nagius/DoubleClock/schematics/doubleClock.kicad_sch

## KiCad design schematics/doubleClock.kicad_sch (2024-07-17)

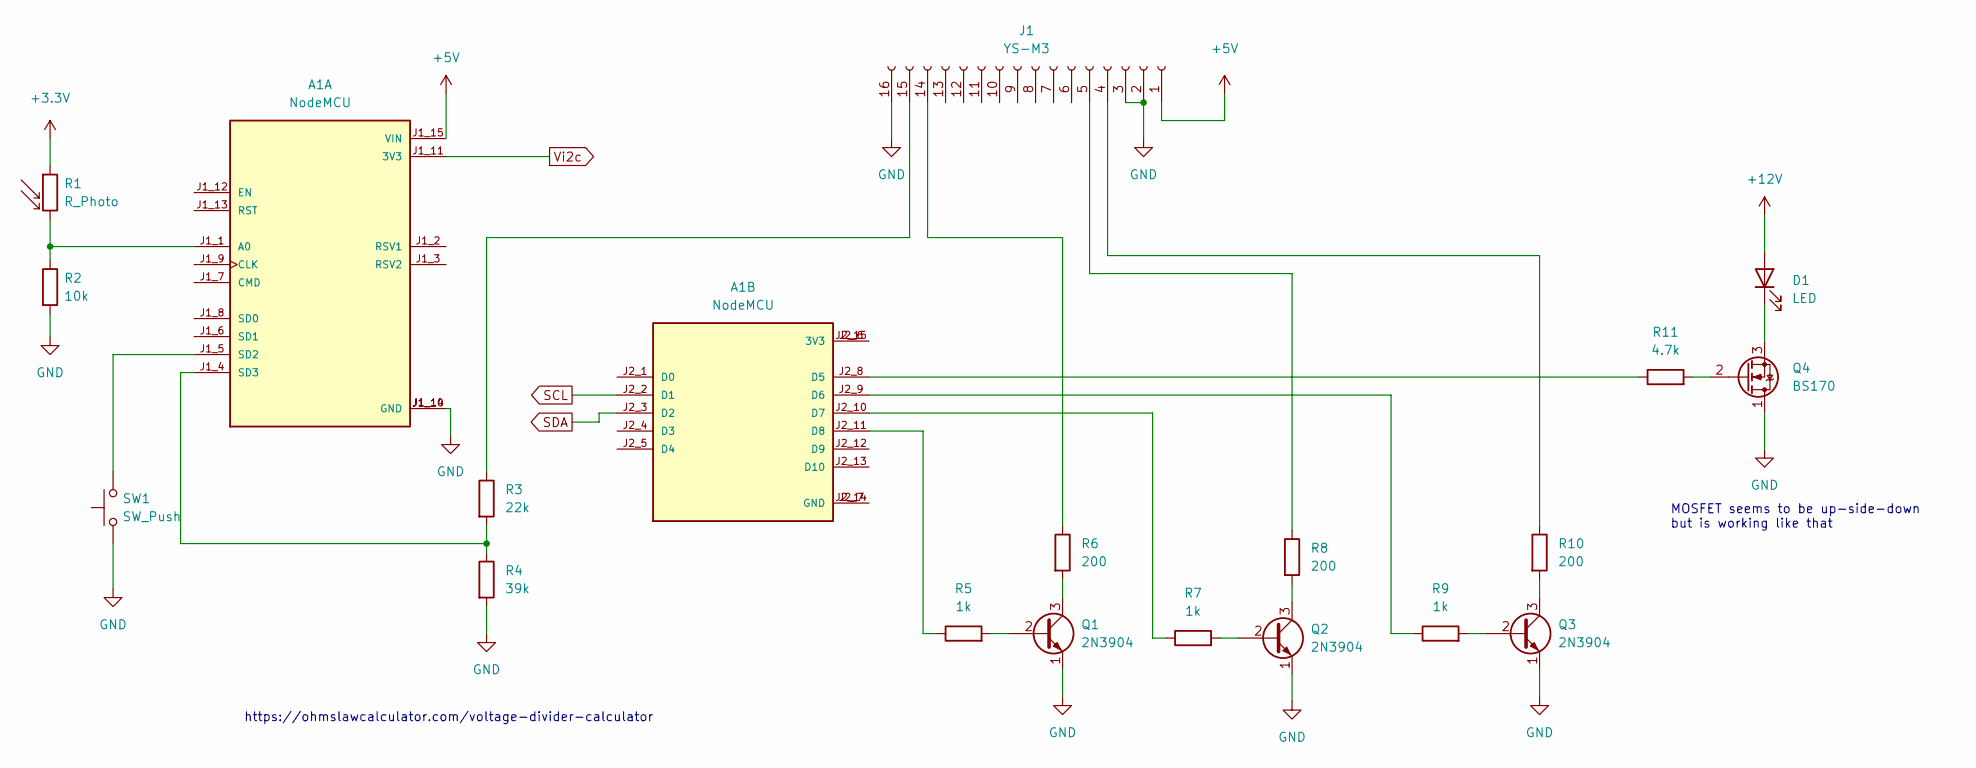
[picture p9: schematic doubleClock.kicad_sch]

Parts:
A1: NodeMCU; SEEED_113990105; PARTREV N/A
D1: LED
J1: YS-M3
Q1, Q2, Q3: 2N3904; TO-92_Inline
Q4: BS170; TO-92_Inline
R1: R_Photo
R2: 10k
R3: 22k
R4: 39k
R5, R7, R9: 1k
R6, R8, R10: 200
R11: 4.7k
SW1: SW_Push

Connections:
+3.3V: R1.1
+5V: A1.J1_15 (VIN), J1.1
+12V: D1.2 (A)
GND: A1.J1_10 (GND), A1.J1_14 (GND), J1.2, J1.3, J1.16, Q1.1 (E), Q2.1 (E), Q3.1 (E), Q4.1 (D), R2.2, R4.2, SW1.1
unnamed: A1.J1_1 (A0), R1.2, R2.1
unnamed: A1.J1_4 (SD3), R3.2, R4.1
unnamed: A1.J1_5 (SD2), SW1.2
unnamed: A1.J2_8 (D5), R11.1
unnamed: A1.J2_9 (D6), R9.1
unnamed: A1.J2_10 (D7), R7.1
unnamed: A1.J2_11 (D8), R5.1
unnamed: A1.J2_7 (GND), A1.J2_14 (GND)
unnamed: A1.J2_6 (3V3), A1.J2_15 (3V3)
unnamed: D1.1 (K), Q4.3 (S)
unnamed: J1.4, R10.1
unnamed: J1.5, R8.1
unnamed: J1.14, R6.1
unnamed: J1.15, R3.1
unnamed: Q1.2 (B), R5.2
unnamed: Q1.3 (C), R6.2
unnamed: Q2.2 (B), R7.2
unnamed: Q2.3 (C), R8.2
unnamed: Q3.2 (B), R9.2
unnamed: Q3.3 (C), R10.2
unnamed: Q4.2 (G), R11.2
SCL: A1.J2_2 (D1)
SDA: A1.J2_3 (D2)
Vi2c: A1.J1_11 (3V3)

Notes on the sheet:
MOSFET seems to be up-side-down but is working like that
https://ohmslawcalculator.com/voltage-divider-calculator
